MSP-code/Morning_Clock/Photos/USB_Holder_Assembly.PNG

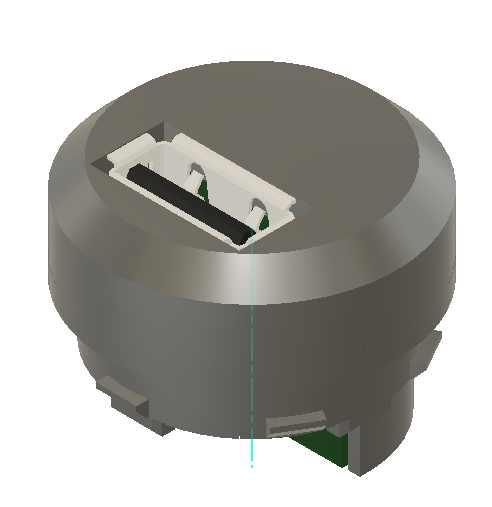
Photos/USB_Holder_Assembly.PNG
